amirbenarbia/episafe/SOLO/EDA/Researches/EDArelaxed.png

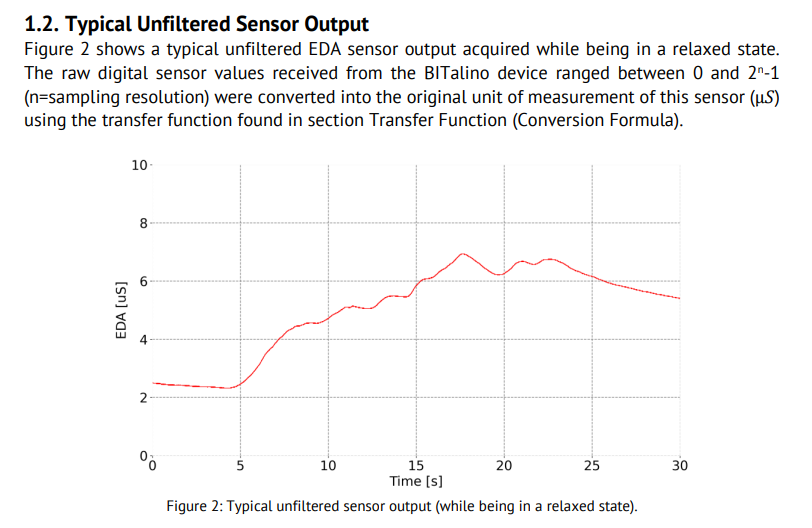
SOLO/EDA/Researches/EDArelaxed.png
