amirbenarbia/episafe/SOLO/EDA/Researches/wrist measurments .png

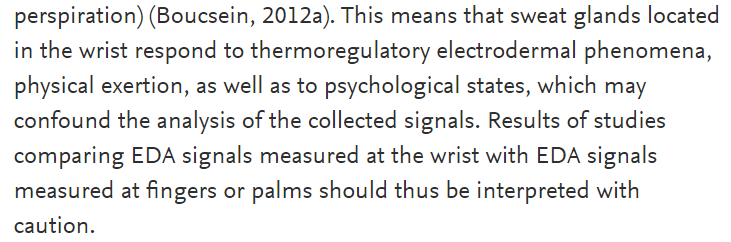
SOLO/EDA/Researches/wrist measurments .png
