amirbenarbia/episafe/SOLO/EDA/Researches/EDA measurement principle .png

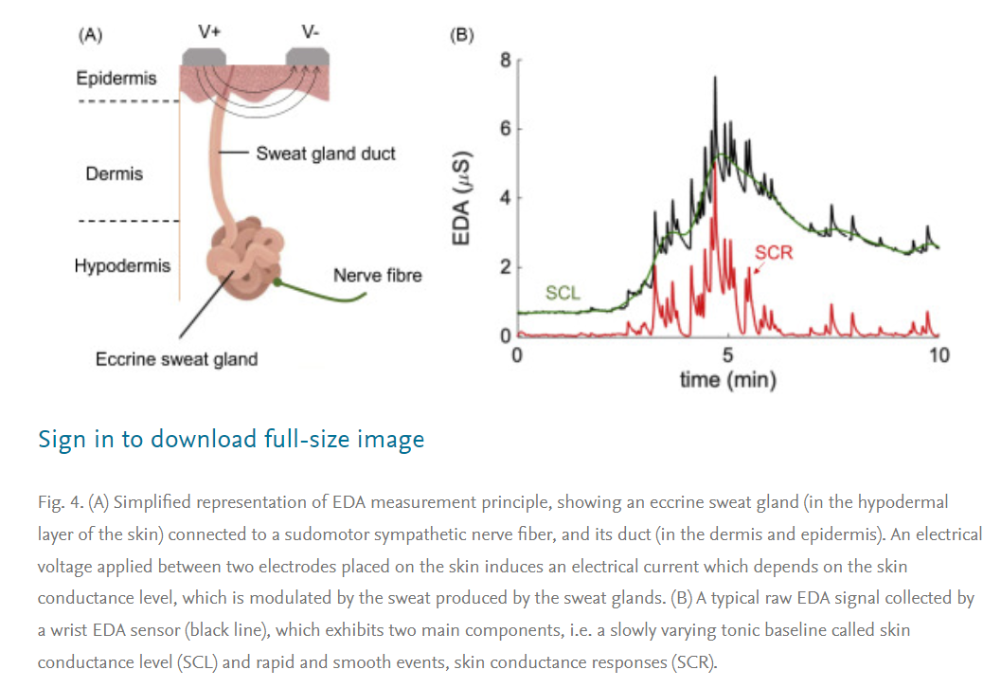
SOLO/EDA/Researches/EDA measurement principle .png
